lucas-wojnarowski/andromeda/Images/andromeda_1.png

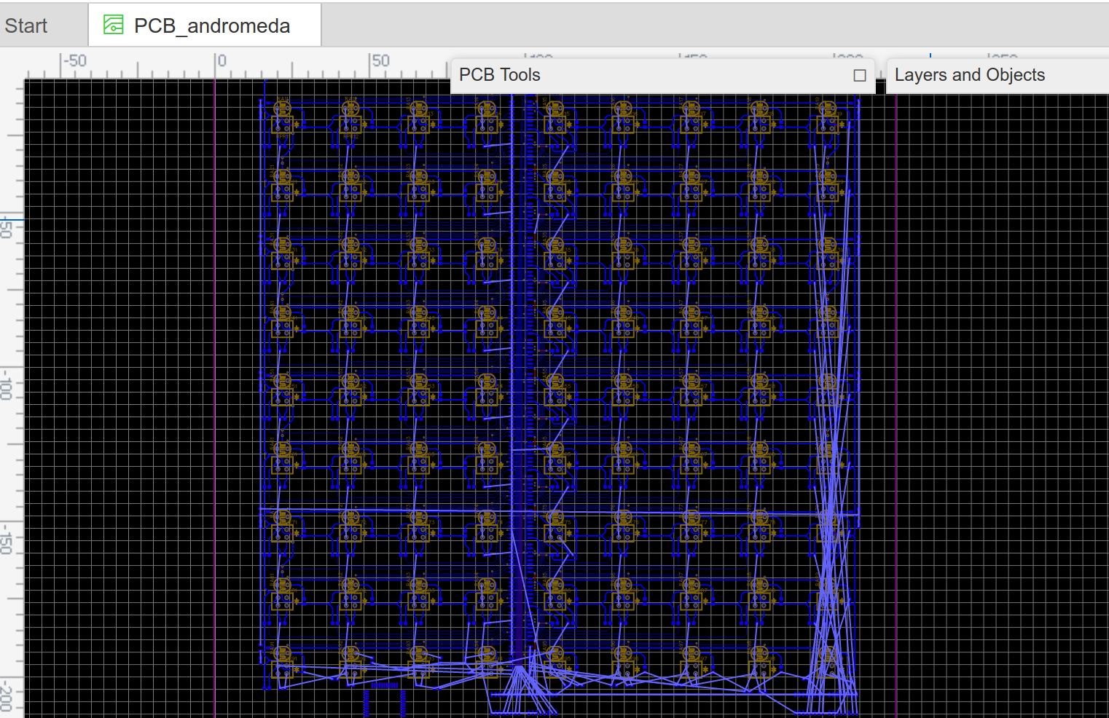
Images/andromeda_1.png
