lucas-wojnarowski/andromeda/Images/andromeda_2.png

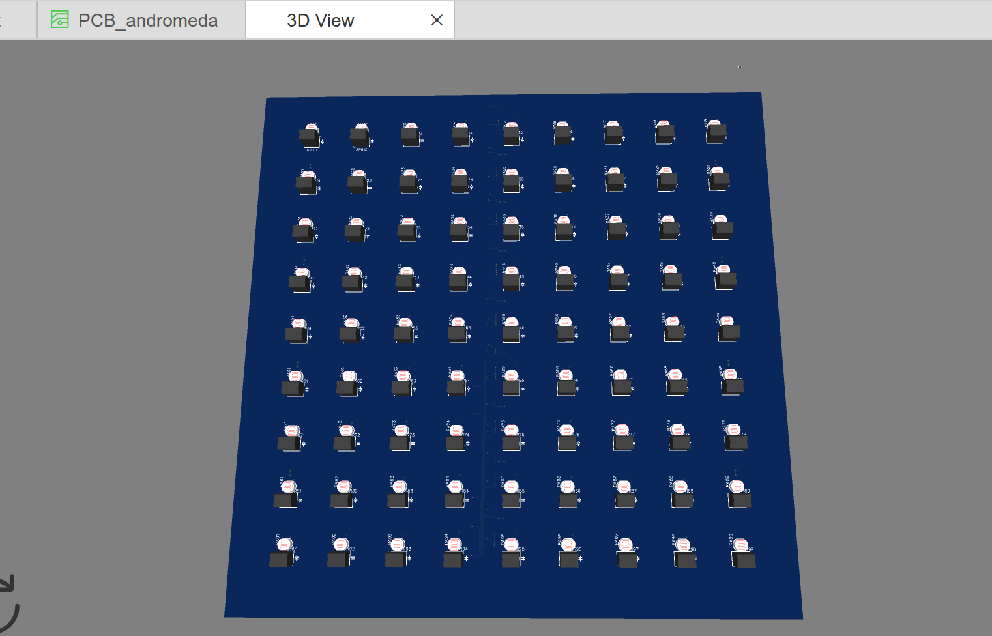
Images/andromeda_2.png
