lucas-wojnarowski/andromeda/Images/andromeda_back.png

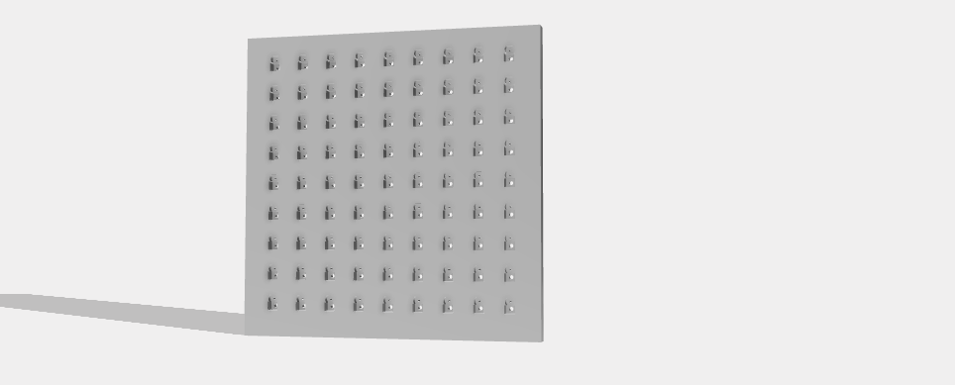
Images/andromeda_back.png
