lucas-wojnarowski/andromeda/Images/andromeda_front.png

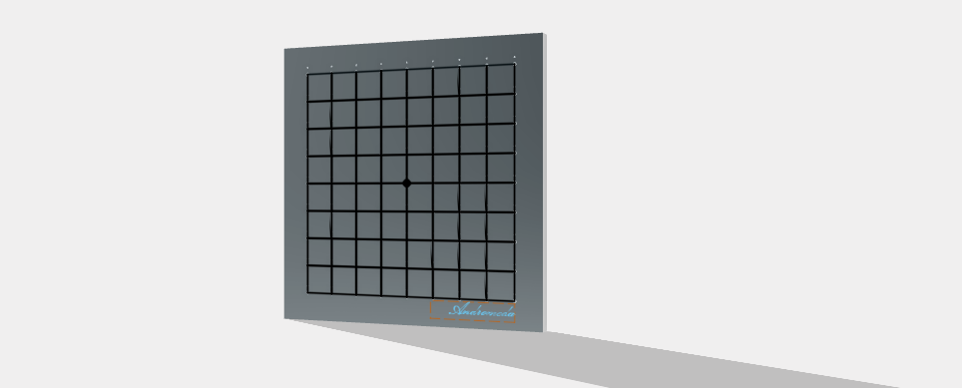
Images/andromeda_front.png
