lucas-wojnarowski/andromeda/Images/aplikacja.png

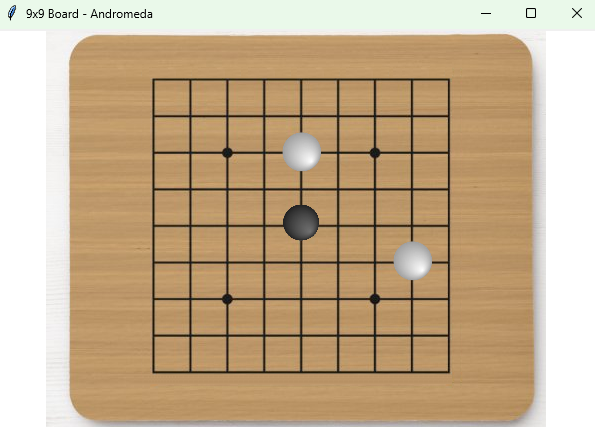
Images/aplikacja.png
