lucas-wojnarowski/andromeda/Images/Plansza.jpg

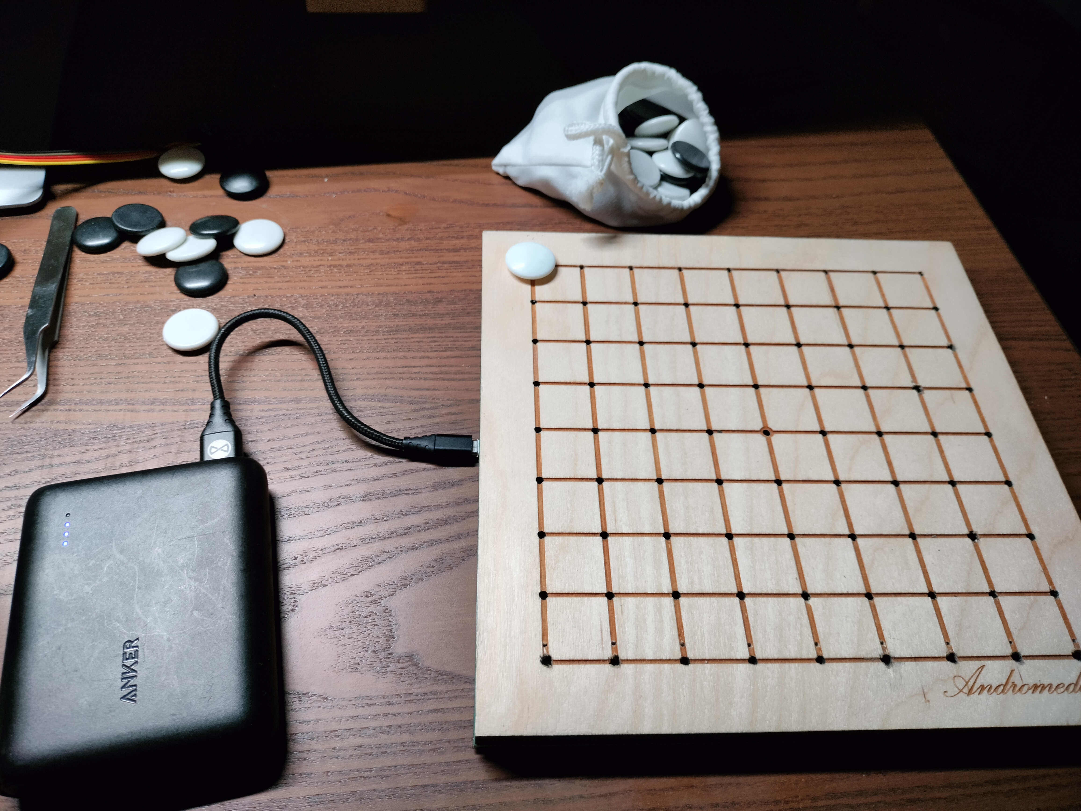
Images/Plansza.jpg
