lucas-wojnarowski/andromeda/Images/Pomiar_polozenie_kamienia.png

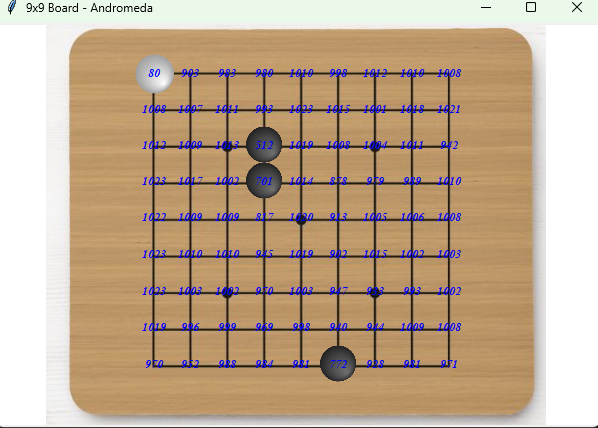
Images/Pomiar_polozenie_kamienia.png
