lucas-wojnarowski/andromeda/Images/Pomiary.png

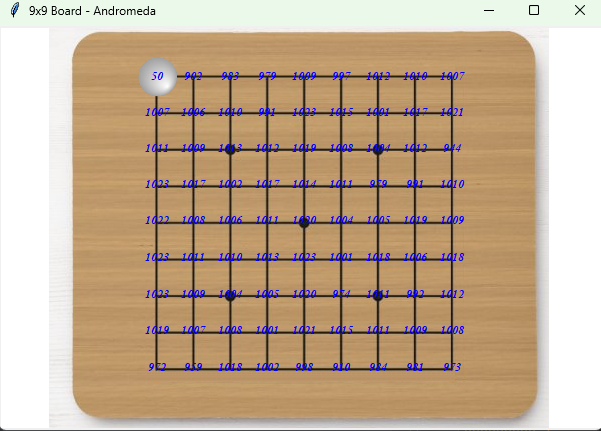
Images/Pomiary.png
