lucas-wojnarowski/andromeda/Images/videokifu.png

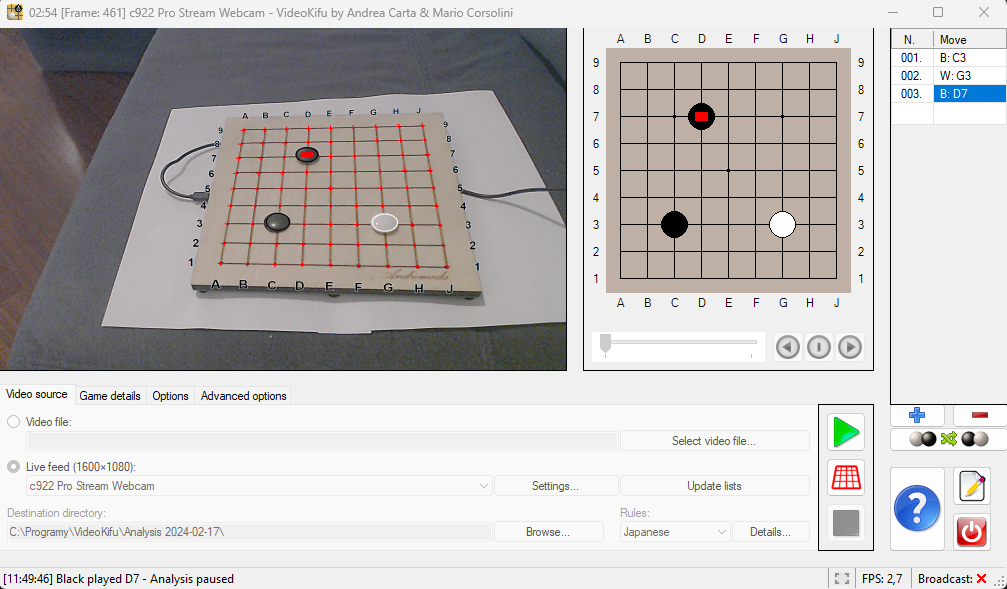
Images/videokifu.png
