lucas-wojnarowski/andromeda/white_stone.png

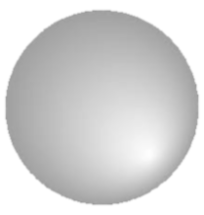
white_stone.png
